KaetzelLab/Open-MAC-opto-ephys-commutator/Open-MAC stl design files/CableAdapter.stl

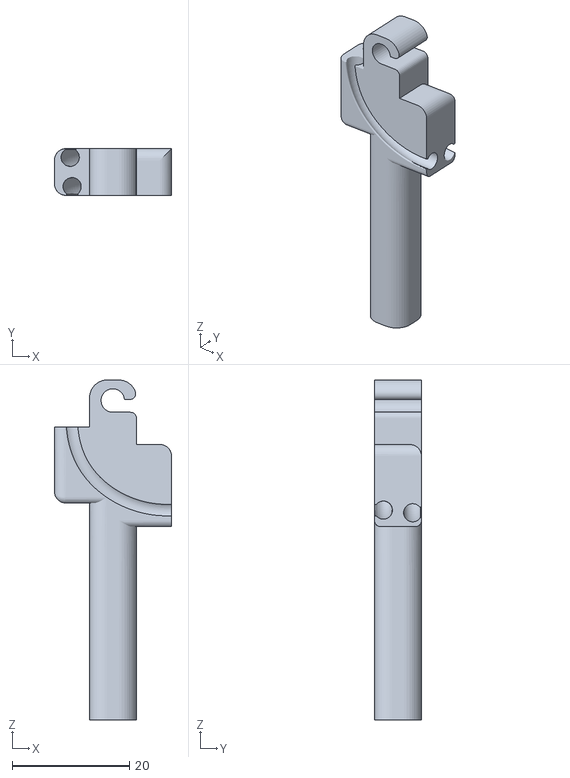
[picture p15: CAD file, 2024-02-28]
Open-MAC stl design files/CableAdapter.stl
20.0 x 8.00 x 58.0
