KaetzelLab/Open-MAC-opto-ephys-commutator/Open-MAC stl design files/Commutator holder.stl

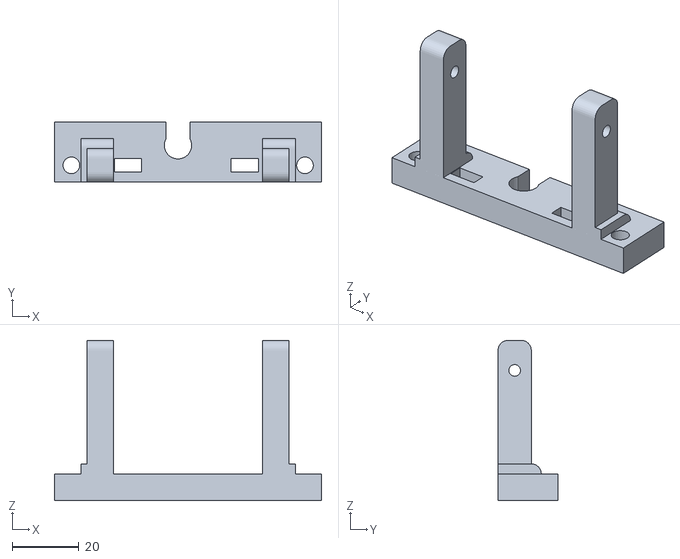
[picture p16: CAD file, 2024-02-28]
Open-MAC stl design files/Commutator holder.stl
80.0 x 18.0 x 48.0
